godders/ahokore-case/pics/height_no_base.jpeg

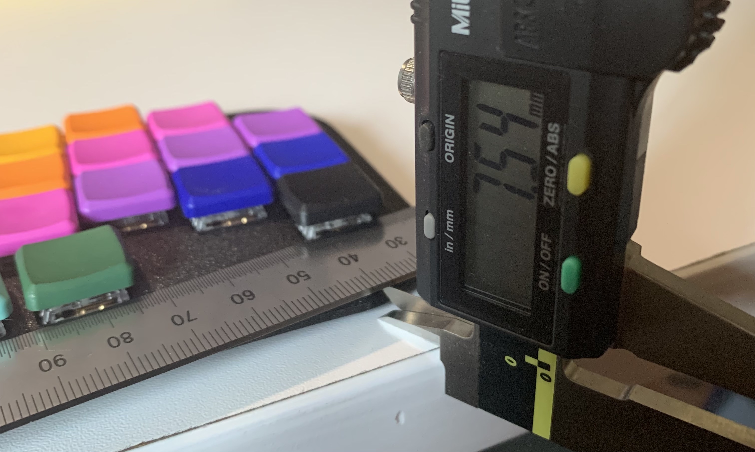
pics/height_no_base.jpeg
